doludiran/Home-Energy-Management-System-/Code/Raspberry pi/car.png

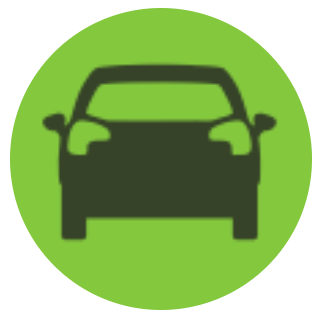
Code/Raspberry pi/car.png
