doludiran/Home-Energy-Management-System-/Code/Raspberry pi/thermostat.png

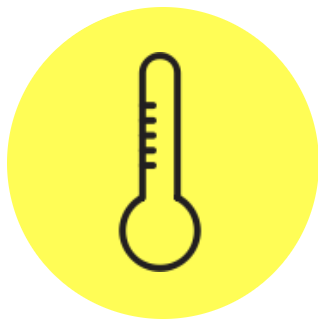
Code/Raspberry pi/thermostat.png
