doludiran/Home-Energy-Management-System-/Code/Raspberry pi/water.png

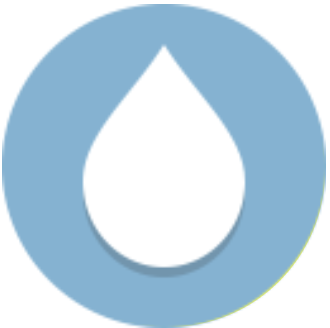
Code/Raspberry pi/water.png
