doludiran/Home-Energy-Management-System-/Code/Raspberry pi/x10.png

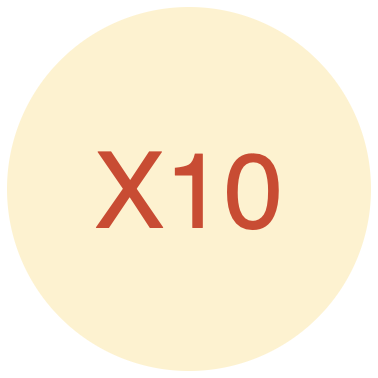
Code/Raspberry pi/x10.png
