doludiran/Home-Energy-Management-System-/Documentation/HEMS Study/Energy Use NRC.JPG

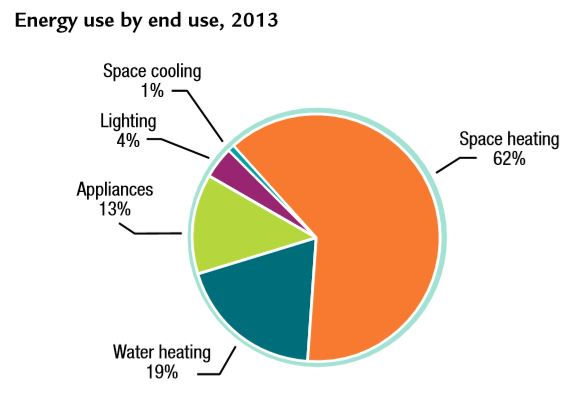
Documentation/HEMS Study/Energy Use NRC.JPG
