doludiran/Home-Energy-Management-System-/Code/CCU pcb/ccu_pcb/ccu_pcb2.kicad_pcb

## KiCad design Code/CCU pcb/ccu_pcb/ccu_pcb2.kicad_pcb (2019-03-17)

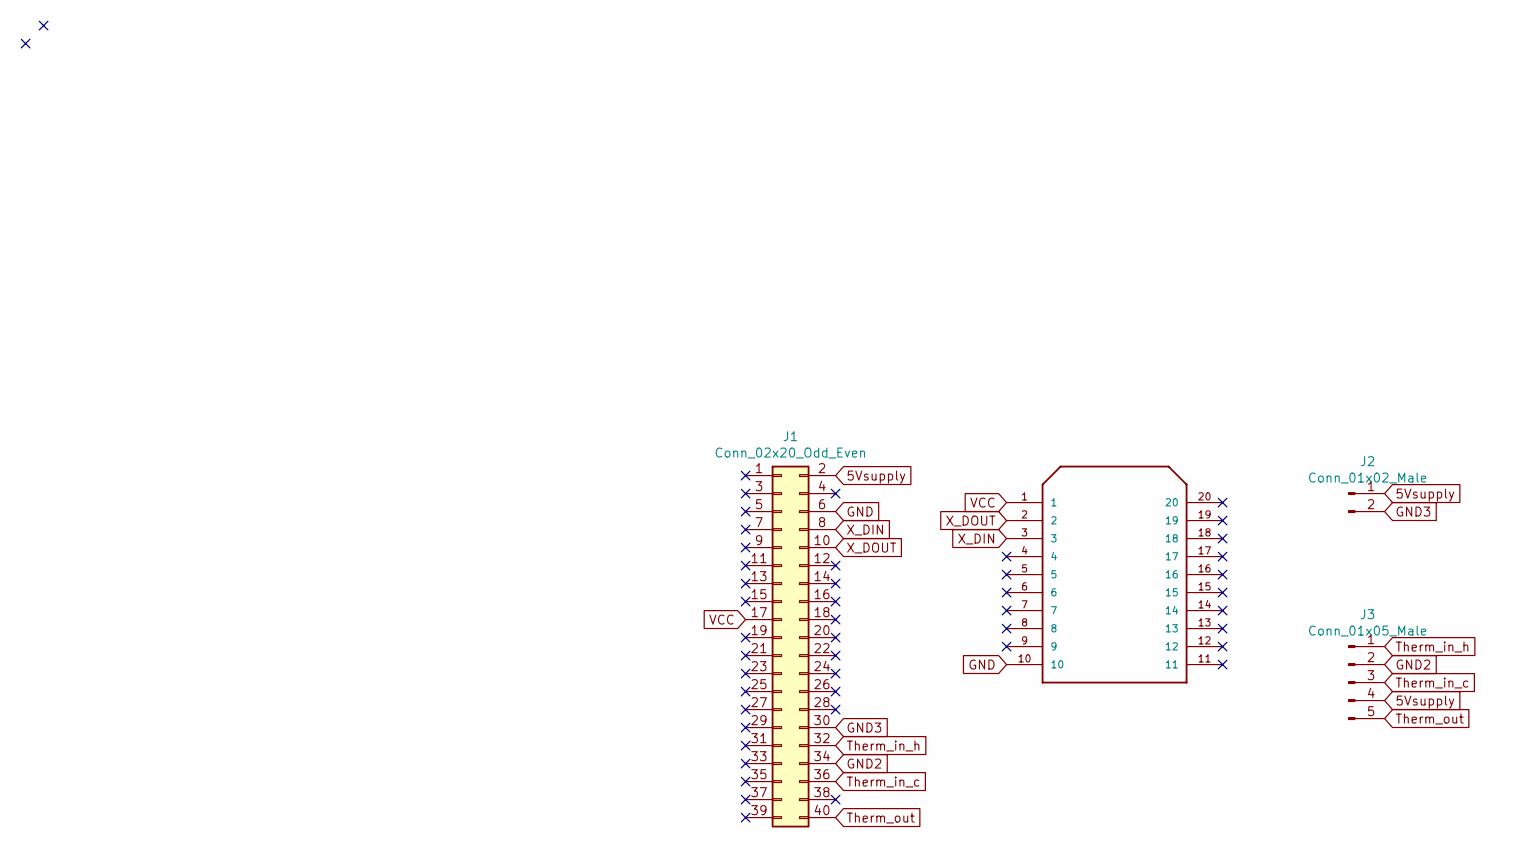
[picture p121: schematic ccu_pcb.sch]

Parts:
J1: Conn_02x20_Odd_Even; PinHeader_2x20_P2.54mm_Vertical
J2: Conn_01x02_Male; PinHeader_1x02_P2.54mm_Vertical
J3: Conn_01x05_Male; PinHeader_1x05_P2.54mm_Vertical
U1: XB24CDMPIT-001; DIP-20

Connections:
5Vsupply: J1.2, J2.1, J3.4
GND: J1.6, U1.10
GND2: J1.34, J3.2
GND3: J1.30, J2.2
Therm_in_c: J1.36, J3.3
Therm_in_h: J1.32, J3.1
Therm_out: J1.40, J3.5
VCC: J1.17, U1.1
X_DIN: J1.8, U1.3
X_DOUT: J1.10, U1.2

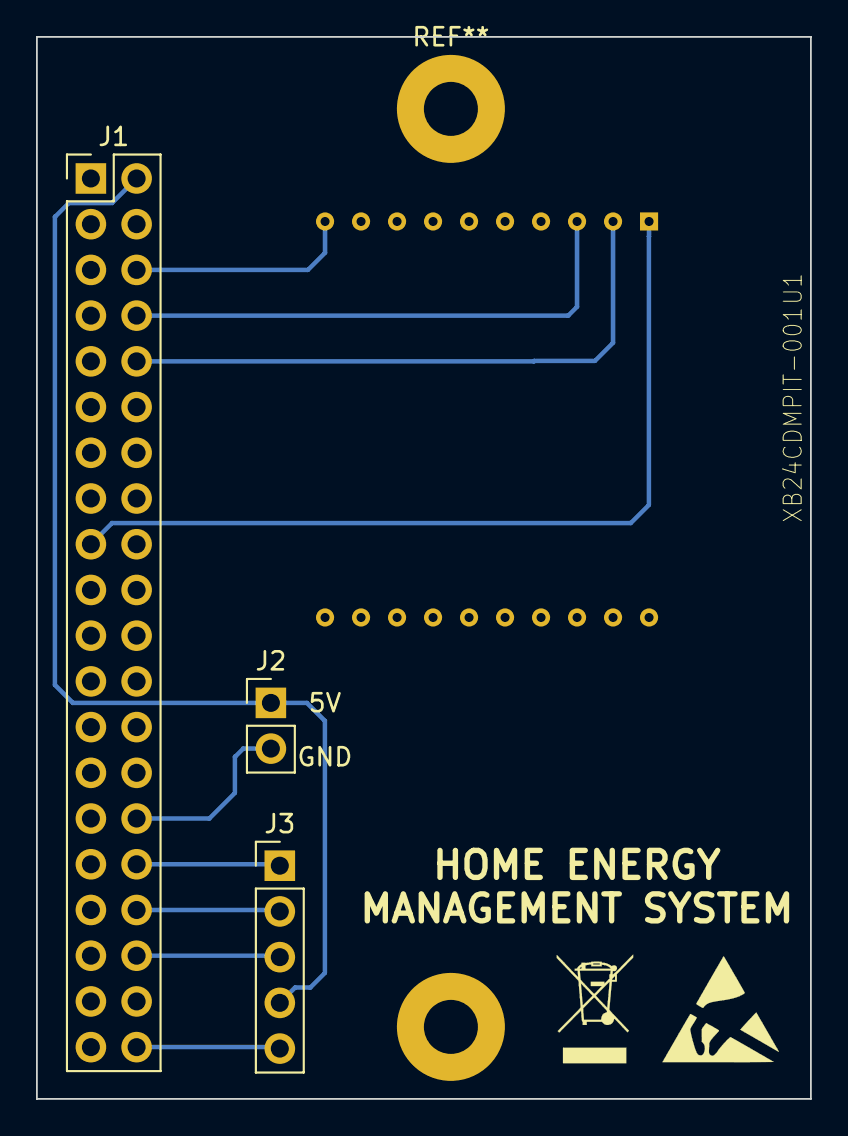
[picture p122: board ccu_pcb2.kicad_pcb from above]

Board: 2 copper layers, 43.0 x 59.0 mm, 4 parts (0 on the bottom side), 10 nets.
