doludiran/Home-Energy-Management-System-/Code/Raspberry pi/tou.py

#################################################################################
# Name: tou.py                                                                  #
# Description: ToU data Retrieval unit                                          #
# Version: V1.1                                                                 #
# Author: Damilola Oludiran                                                     #
#                                                                               #
#                                                                               #
# This software is supplied "AS IS" without warranties of any kind.             #
#                                                                               #
#----------------------------------------------------------------------------   #
# History:                                                                      #
#            V1.0 Initial Version by Damilola Oludiran                          #
#            V1.1 Changed implementation to threaded class by Damilola Oludiran #
#                                                                               #
#################################################################################

#################################################################################
# Imports                                                                       #
#################################################################################

import threading
import queue as Queue
from time import sleep
import requests
import json
import pandas as pd
import datetime as DT

Total_Daily_Minutes =1440
DR_interval = 15
minutes = 60

#################################################################################
# ToU Thread Class                                                              #
#################################################################################

class ToU(threading.Thread):
    rxQueue = Queue.Queue(maxsize=1)
    stop = threading.Event()
    
    #################################################################################
    # Name: __init__                                                                #
    # Parameters: self                                                              #
    # Description: This method initialises the thread                               #
    # Preconditions: Internet access is configured                                  #
    # Postconditions: Thread starts                                                 #
    #################################################################################
    def __init__(self):
        threading.Thread.__init__(self)
        self.start()
    
    
    #################################################################################
    # Name: shutdown                                                                #
    # Parameters: self                                                              #
    # Description: This method terminates the thread                                #
    # Preconditions:n/a                                                             #
    # Postconditions: Thread stops running                                          #
    #################################################################################
    def shutdown(self):
        self.stop.set()
        self.join()
    
    #################################################################################
    # Name: run                                                                     #
    # Parameters: self                                                              #
    # Description: This method is the thread's main loop                            #
    # Preconditions: n/a                                                            #
    # Postconditions: Continuously retrieves tou data                               #
    #################################################################################
    def run(self):
        while not self.stop.is_set():
            self.getToU()
            sleep(0.1)

    #################################################################################
    # Name: recieveTemp                                                             #
    # Parameters: self                                                              #
    # Description: This method returns the tou data                                 #
    # Preconditions: rxQueue is initialised                                         #
    # Postconditions: returns queue data if any                                     #
    #################################################################################
    def recieveTOU(self):
        if not self.rxQueue.empty():
            return self.rxQueue.get()
        else:
            return 0

    #################################################################################
    # Name: converttomins                                                           #
    # Parameters: self, time and format of the time                                 #
    # Description: This method returns total minutes as interger                    #
    # Preconditions: n/a                                                            #
    # Postconditions: returns total time in minutes                                 #
    #################################################################################
    def converttomins(self, timevalue, timeformat):
        t1 = DT.datetime.strptime(timevalue, timeformat)
        t2 = DT.datetime(1900,1,1)
        totalminutes = (t1-t2).total_seconds()/minutes
        return totalminutes

    #################################################################################
    # Name: retrieveToU                                                             #
    # Parameters: self                                                              #
    # Description: This method returns the tou                                      #
    # Preconditions: internet connection is set up                                  #
    #                ToU data is available in the expected format                   #
    # Postconditions: returns tou data if any                                       #
    #################################################################################
    def retrieveToU(self):
        tou=requests.get('http://www2.cs.uregina.ca/~joshi26a/utility portal/tou_json/tou_json.json').json()
        tou_d = tou[0]
        i = 1
        tou_df = []
        while i < len(tou_d):
            tou_df.append(tou_d[i])
            i+=1
        
        i = 0
        while i < len(tou_df):
            totalFromminutes = self.converttomins(tou_df[i]['TOU From'], '%H:%M:%S')
            totalTominutes = self.converttomins(tou_df[i]['TOU To'], '%H:%M:%S')
            if (i == (len(tou_df) - 1 ) and (tou_df[i]['TOU To'] == '00:00:00')):
                diff = Total_Daily_Minutes-totalFromminutes
            else:
                diff = abs(totalTominutes - totalFromminutes)
            diff2 = diff
            diff = diff/DR_interval
            tou_df[i]['Total Minutes'] = diff
            tou_df[i]['Total Minutes p'] = diff2
            i+=1
        return tou_df
    
    #################################################################################
    # Name: getToU                                                                  #
    # Parameters: self                                                              #
    # Description: This method returns the tou in arrays of different formats as    #
    #              required by different functions in the main application          #
    # Preconditions: internet connection is set up                                  #
    #                ToU data is available in the expected format                   #
    # Postconditions: returns tou data in queue if any                              #
    #################################################################################
    def getToU(self):
        
        data = self.retrieveToU()
        
        price = []
        price2 = []
        time_of_use = []
        onpeakprice = 0
        midpeakprice = 0
        offpeakprice = 0
        tou_data = []
        plotdata = []
        i = 0
        while i < len(data):
            j = 0
            k = 0
            max = int(data[i]['Total Minutes'])
            max2 = int(data[i]['Total Minutes p'])
            while j < max:
                price.append(int(data[i]['TOU Price']))
                j+=1
            if (data[i]['TOU Period'] == 'ON-Peak'):
                time_of_use.append('#e74c3c')
                onpeakprice = data[i]['TOU Price']
            elif (data[i]['TOU Period'] == 'MID-Peak'):
                time_of_use.append('#e7a23c')
                midpeakprice = data[i]['TOU Price']
            elif (data[i]['TOU Period'] == 'OFF-Peak'):
                time_of_use.append('#2ecc71')
                offpeakprice =data[i]['TOU Price']
            while k < max2:
                price2.append(int(data[i]['TOU Price']))
                k+=1
            plotdata.append(max)
            i+=1
        tou_data.append(plotdata)
        tou_data.append(time_of_use)
        tou_data.append(price)
        tou_data.append(price2)
        tou_data.append(onpeakprice)
        tou_data.append(offpeakprice)
        tou_data.append(midpeakprice)
        self.rxQueue.put(tou_data)
