doludiran/Home-Energy-Management-System-/Code/PowerMonitoring/ADC_INIT.c

/**
// Header format used with permission from Damilola Oludiran
 ******************************************************************************
 * Name: ADC_INIT.c
 * Description: ADC initialization and other ADC functions
 * Version: V1.0
 * Author: Bikramjit Saini 
  
 *
 * This software is supplied "AS IS" without warranties of any kind.
 *
 *
 *----------------------------------------------------------------------------
 * History:
 *          V1.0 Initial Version by Bikramjit Saini
 *            
 *         
 *****************************************************************************
 */

#include "stm32f10x.h"
#include "IOdef.h"
#include "ADC_INIT.h"
 
 /* Function to initialize the ADC system on STM32F100RB
Input: none
Return: none
 */
 void Init_ADC(void)
{
		// enable clock for IO port A and ADC1 interface
	RCC->APB2ENR |=  RCC_APB2ENR_IOPAEN | RCC_APB2ENR_ADC1EN;

	GPIOA->CRL &= ~(GPIO_CRL_CM0 | GPIO_CRL_CM1 ); 
	GPIOA->CRL |= (GPIO_CRL_CM0_AN | GPIO_CRL_CM1_AN);
		
	// Calibrate ADC
	ADC1-> CR2 |= ADC_CR2_CAL ;

	// turn ADC 'on'
	ADC1-> CR2 |=	ADC_CR2_ADON;

	//select sampling time 
	ADC1-> SMPR2 |= ((uint32_t)0x0000000F) | ((uint32_t)0x00000030); 
}

//----------------------------------------------------------------------------------//


/* Function to select the ADC channel
Input: Integer value corresponding to the ADC channel to be used
Return: None
*/
void ADC_start(int channel)
{ 
	// Selecting channel 
	ADC1->SMPR2 |= 0X3f;
	
	ADC1->SQR3 &= ~ADC_SQR3_SQ1;
	ADC1 -> SQR3 = channel; 
	
	// Start the conversion	
	ADC1-> CR2 = ADC_CR2_ADON; 
	delay(2000);
}


//----------------------------------------------------------------------------------//


/* Function to read the ADC data
Input: none
Return: integer value
*/
int Read_ADC()
{	
	while((ADC1->SR & ADC_SR_EOC) != ADC_SR_EOC)
	{
	}
	return (ADC1->DR & ADC_DR_DATA);
}


//----------------------------------------------------------------------------------//


/* Function to convert Raw ADC data to a voltage value
Input: Raw ADC value read by Read_ADC() function
Return: integer value
*/
int Power_Reading_Res(uint16_t value)
{
	int val = (3300*value)/4095;   
																								
	return (val);		
}


//----------------------------------------------------------------------------------//


/* Function to add a delay
Input: 32 bit integer for delay counter (12000 will give 2 ms delay)
Return: none
References: Provided by Dave Duguid in ENEL 387 Lab
*/
void delay(uint32_t count)
{
	int i=0;
	for(i=0; i< count; ++i)
	{
	}
}

// Reference: The code was written under the guidance of Dave Duguid in ENEL 387 lab
