doludiran/Home-Energy-Management-System-/Code/PowerMonitoring/Clocks.c

// Reference : Taken from "lab1_lib.c" provided by Dave Duguid in ENEL 387.


#include "stm32f10x.h"
#include "clocks.h"


void clockInit(void)
{
    uint32_t temp = 0x00;
    
    RCC->CFGR = 0x00050002;     // Output PLL/2 as MCO,
                                // PLLMUL X3, PREDIV1 is PLL input

    RCC->CR =  0x01010081;      // Turn on PLL, HSE, HSI

    while (temp != 0x02000000)  // Wait for the PLL to stabilize
    {
        temp = RCC->CR & 0x02000000; //Check to see if the PLL lock bit is set
    }
}
